AlicDanclic/KeyBoard/Software/Main_KeyBoard/Core/Inc/main.h

#define CE_Pin GPIO_PIN_3
#define CE_GPIO_Port GPIOB
#define PL_Pin GPIO_PIN_4
#define PL_GPIO_Port GPIOB
